kaibs/Boombox/cad_v2/boombox_v1.FCStd

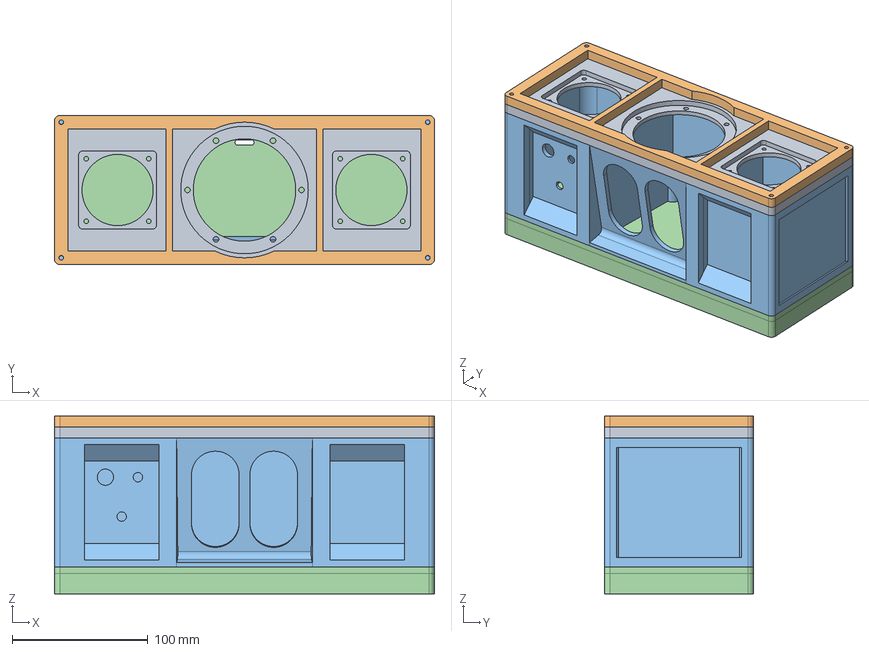
[picture p15: CAD file, 2021-06-10, an earlier design]
cad_v2/boombox_v1.FCStd
280.0 x 110.0 x 131.0 mm
front plate
front frame
main frame
back compartment
